Uncapped-Potential/fun-fitness-firmware/enclosure_3D_models/print orientation photos and settings/usb-c port support painting.png

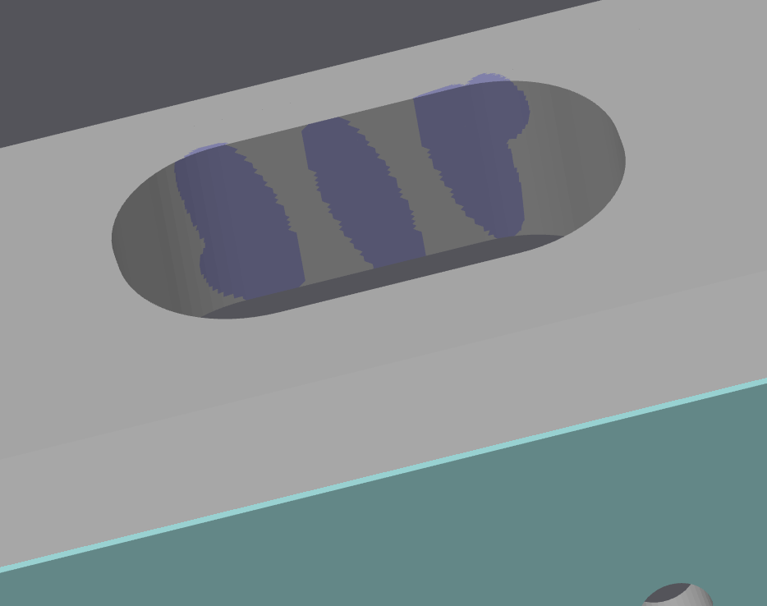
enclosure_3D_models/print orientation photos and settings/usb-c port support painting.png
